erellaz/seisberry/Pi_support.scad

$fn=100;

difference(){
cube([20,20,10],true);
translate([0,0,-10]) cylinder(20,r=1.0,true);
}
